gowenrw/astable_badge/art/2021-1.jpg

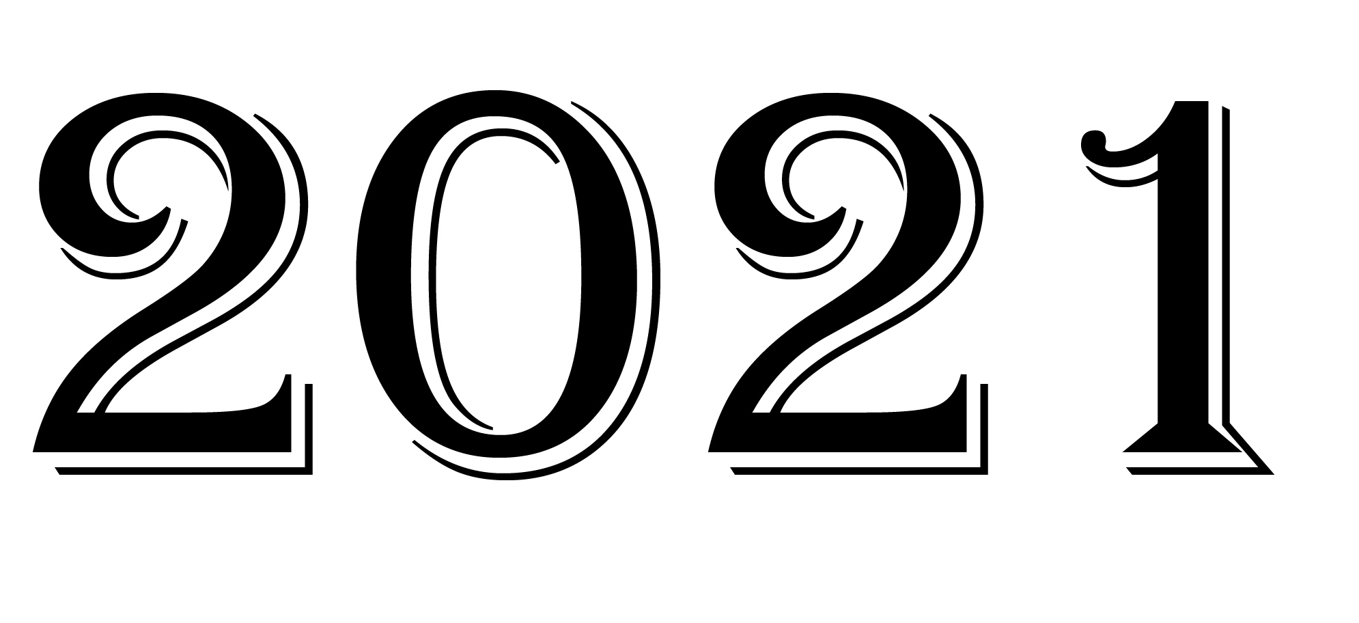
art/2021-1.jpg
