gowenrw/astable_badge/art/CyberDolphin-1-01.jpg

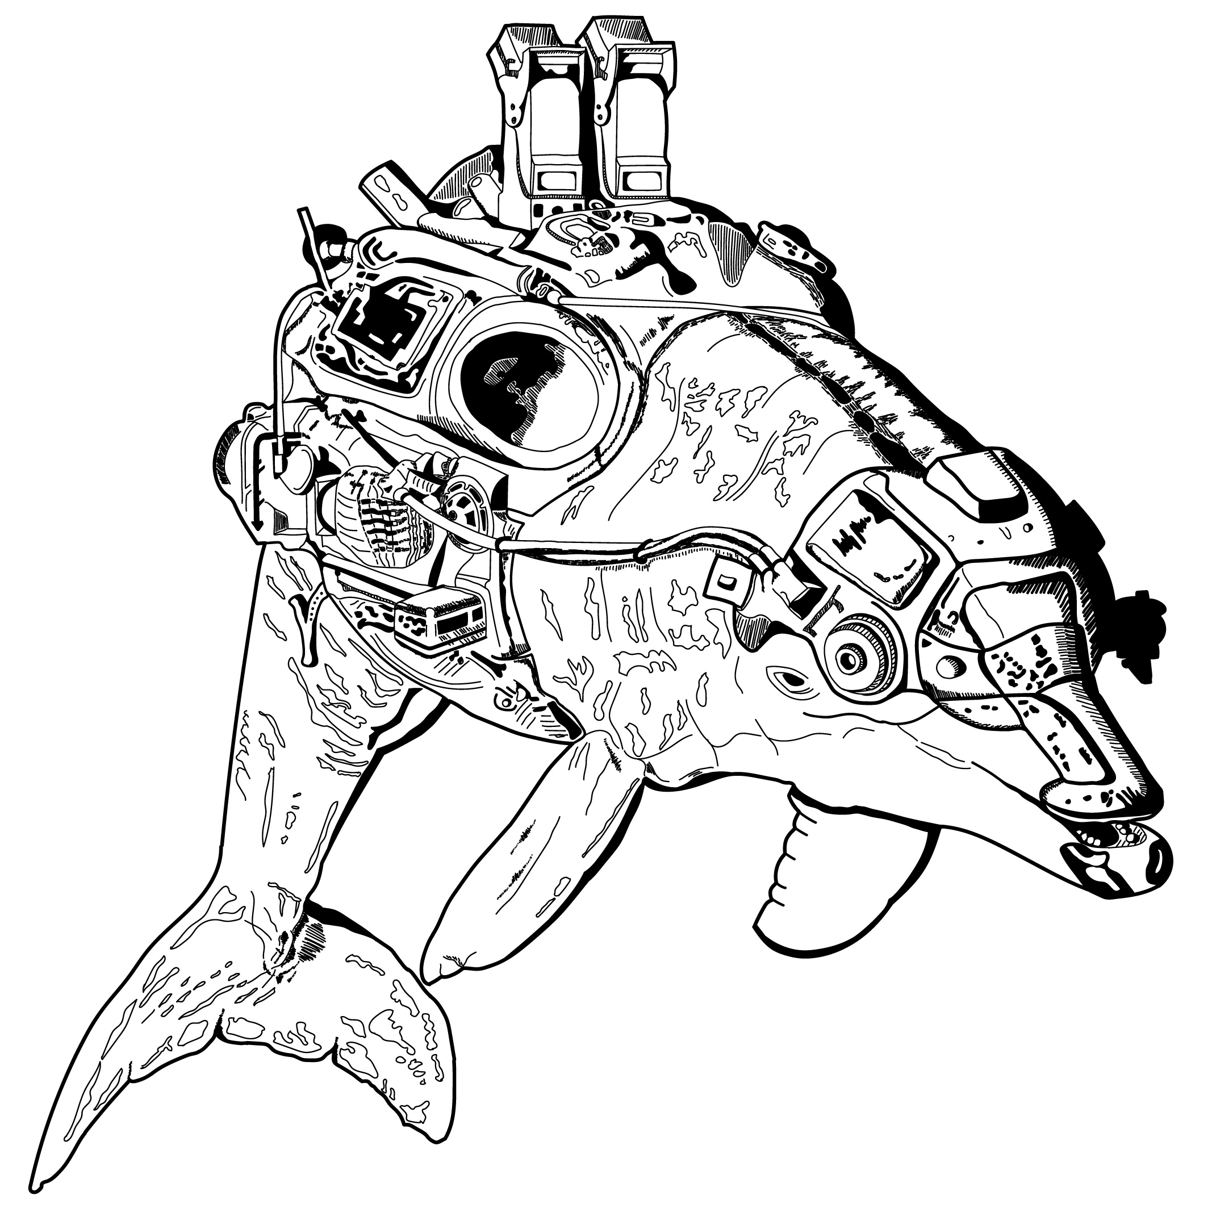
art/CyberDolphin-1-01.jpg
