gowenrw/astable_badge/art/inspiration/CyberDolphin.jpg

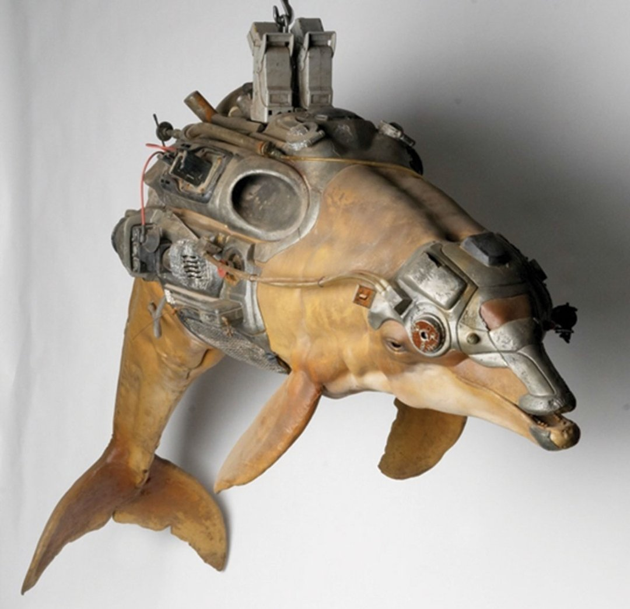
art/inspiration/CyberDolphin.jpg
