gowenrw/astable_badge/art/Lanyard-1-01.jpg

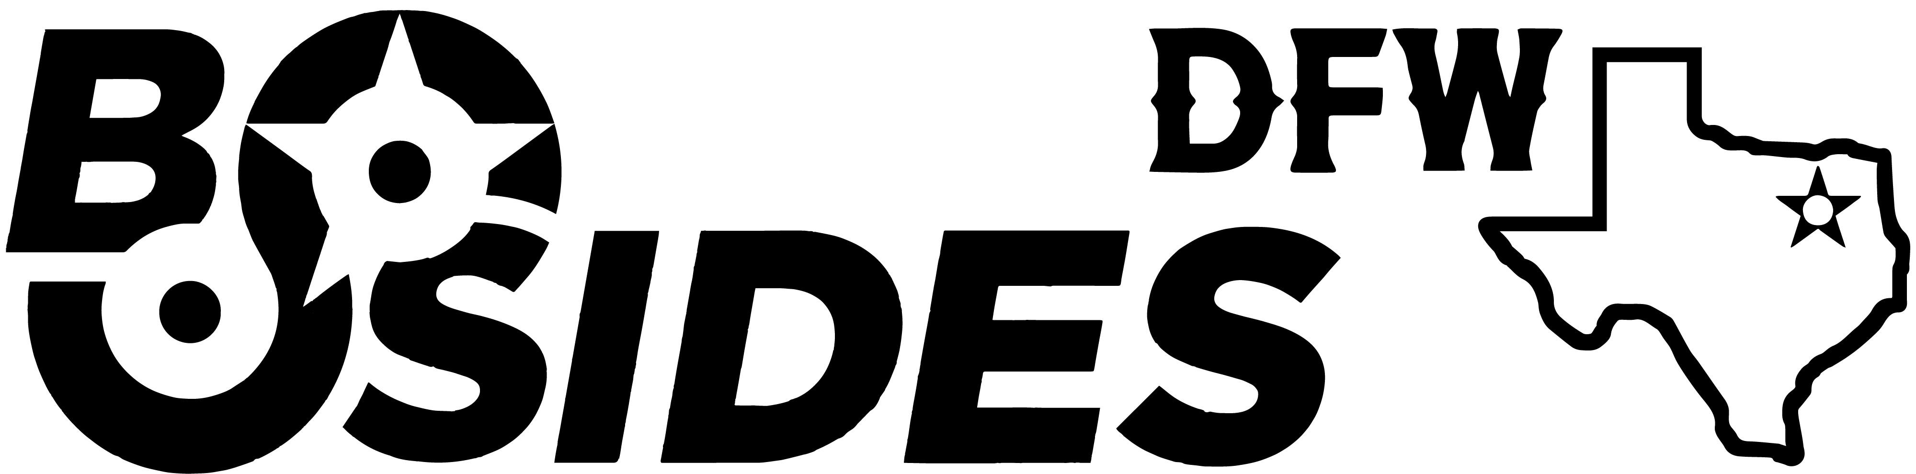
art/Lanyard-1-01.jpg
