gowenrw/astable_badge/eda/astable_dev/snapshots/astable_dev_3D_01.png

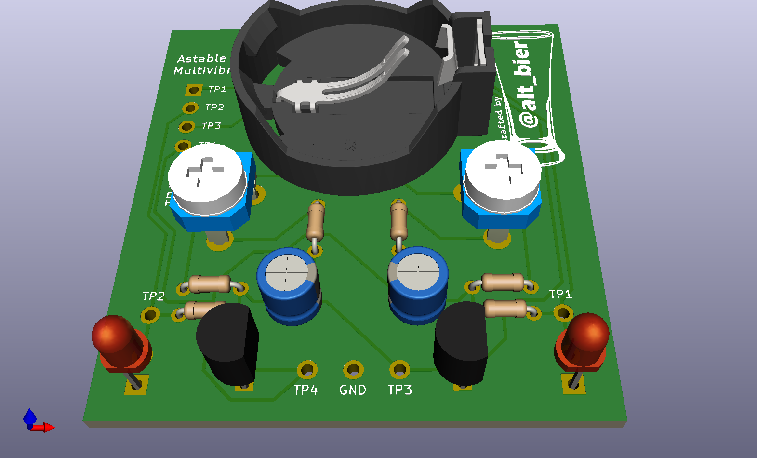
eda/astable_dev/snapshots/astable_dev_3D_01.png
