gowenrw/astable_badge/eda/astable_dev/3d_models/CP_Radial_D6.3mm_P2.50mm.step

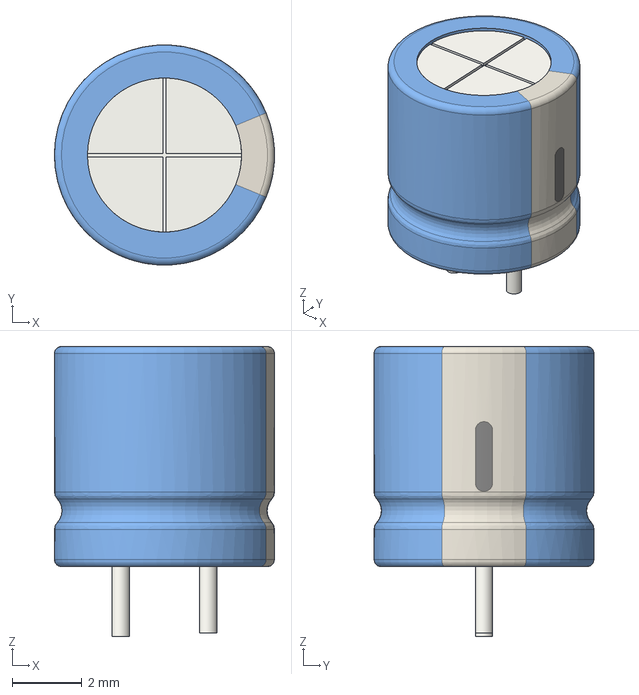
[picture p72: CAD file, 2021-08-17]
eda/astable_dev/3d_models/CP_Radial_D6.3mm_P2.50mm.step
6.30 x 6.30 x 8.30 mm
