gowenrw/astable_badge/eda/astable_badge/3d_models/PinHeader_1x05_P2.54mm_Vertical.step

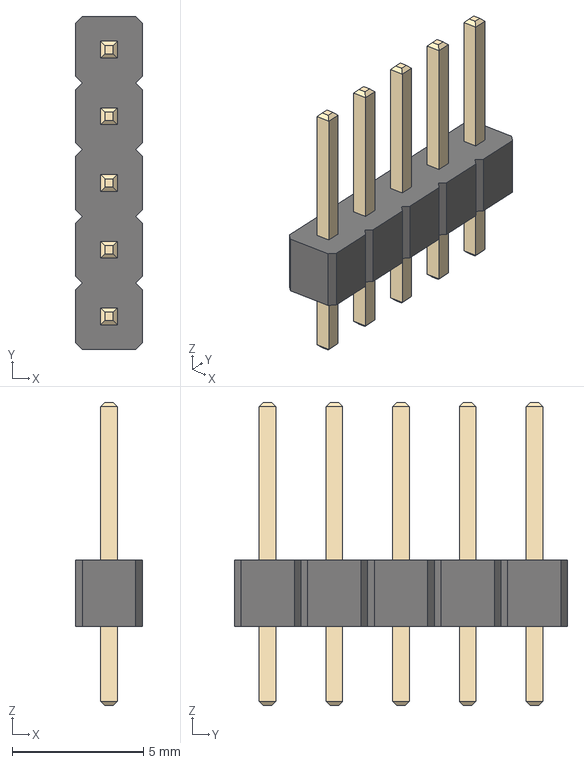
[picture p73: CAD file, 2021-08-19]
eda/astable_badge/3d_models/PinHeader_1x05_P2.54mm_Vertical.step
2.54 x 12.7 x 11.5 mm
