gowenrw/astable_badge/eda/astable_dev/3d_models/LED_D5.0mm-4_RGB.step

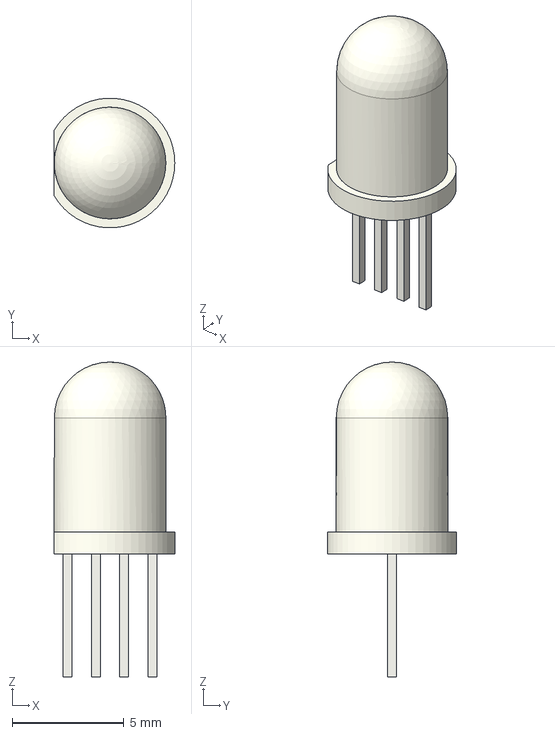
[picture p74: CAD file, 2021-08-17]
eda/astable_dev/3d_models/LED_D5.0mm-4_RGB.step
5.40 x 5.79 x 14.1 mm
