gowenrw/astable_badge/eda/astable_badge/3d_models/PinSocket_1x05_P2.54mm_Vertical.step

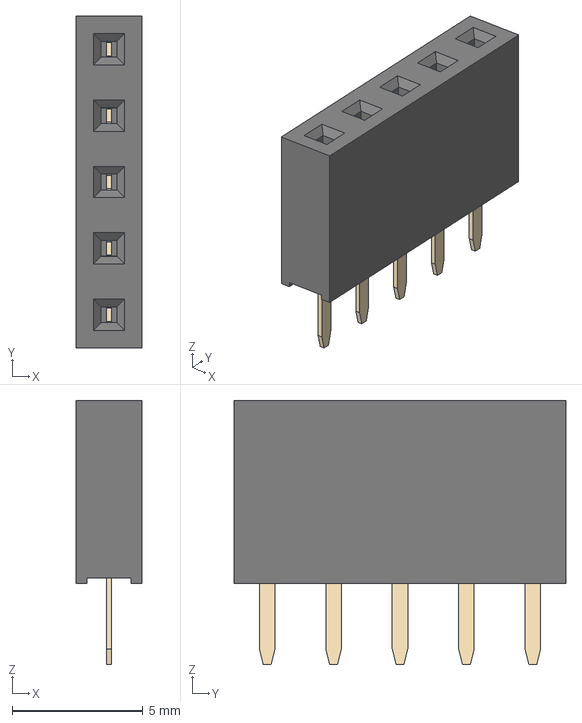
[picture p75: CAD file, 2021-08-19]
eda/astable_badge/3d_models/PinSocket_1x05_P2.54mm_Vertical.step
2.54 x 12.7 x 10.1 mm
