gowenrw/astable_badge/eda/astable_dev/3d_models/SW_SPDT_PCM12.step

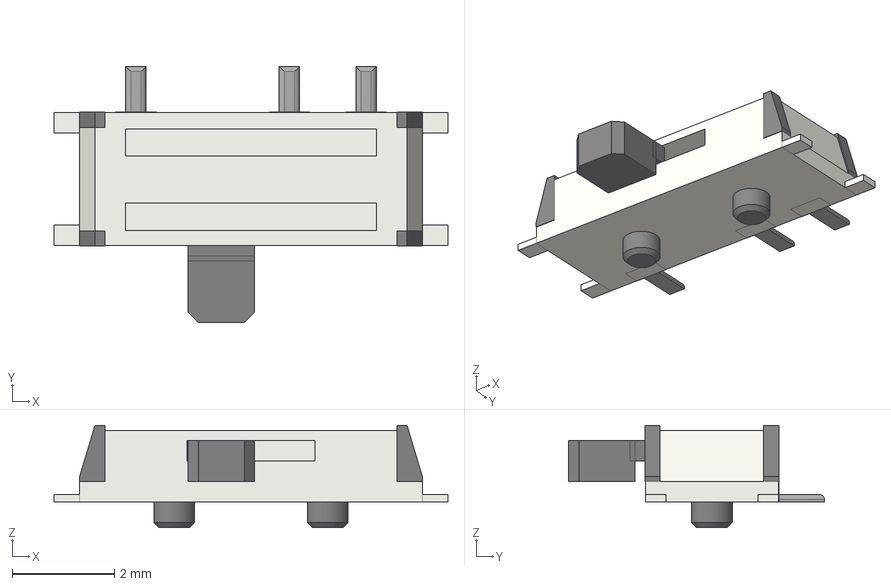
[picture p76: CAD file, 2021-08-17]
eda/astable_dev/3d_models/SW_SPDT_PCM12.step
7.70 x 5.00 x 2.00 mm
