gowenrw/astable_badge/eda/astable_badge/3d_models/PinHeader_1x01_P2.54mm_Horizontal.step

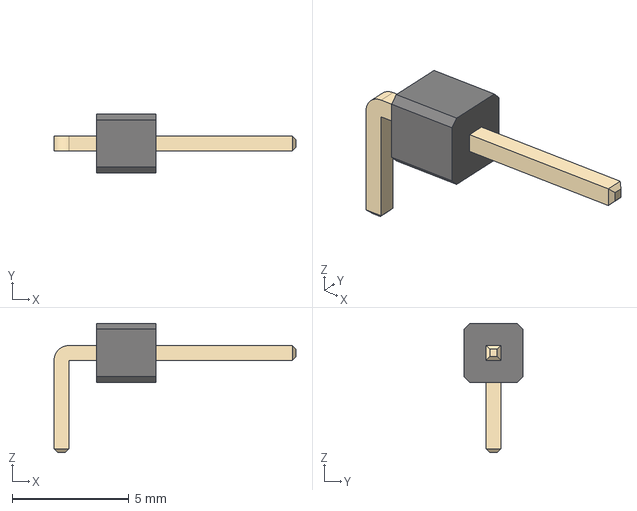
[picture p77: CAD file, 2021-08-19]
eda/astable_badge/3d_models/PinHeader_1x01_P2.54mm_Horizontal.step
10.4 x 2.54 x 5.54 mm
