gowenrw/astable_badge/eda/astable_badge/3d_models/PinSocket_1x05_P2.54mm_Horizontal.step

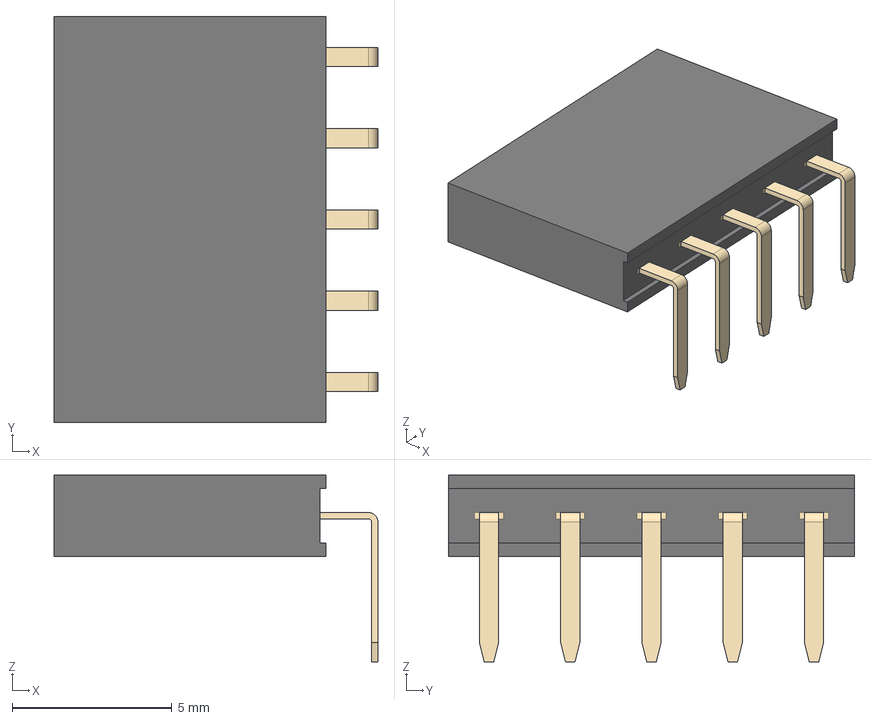
[picture p79: CAD file, 2021-08-19]
eda/astable_badge/3d_models/PinSocket_1x05_P2.54mm_Horizontal.step
10.1 x 12.7 x 5.84 mm
