gowenrw/astable_badge/eda/astable_dev/3d_models/LED_D5.0mm.step

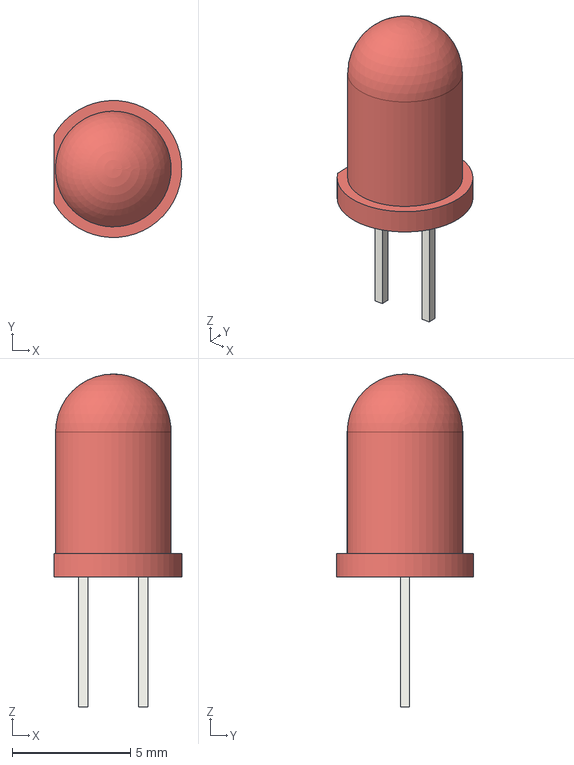
[picture p80: CAD file, 2021-08-17]
eda/astable_dev/3d_models/LED_D5.0mm.step
5.40 x 5.79 x 14.1 mm
