gowenrw/astable_badge/eda/astable_badge/3d_models/TO-92_Inline.step

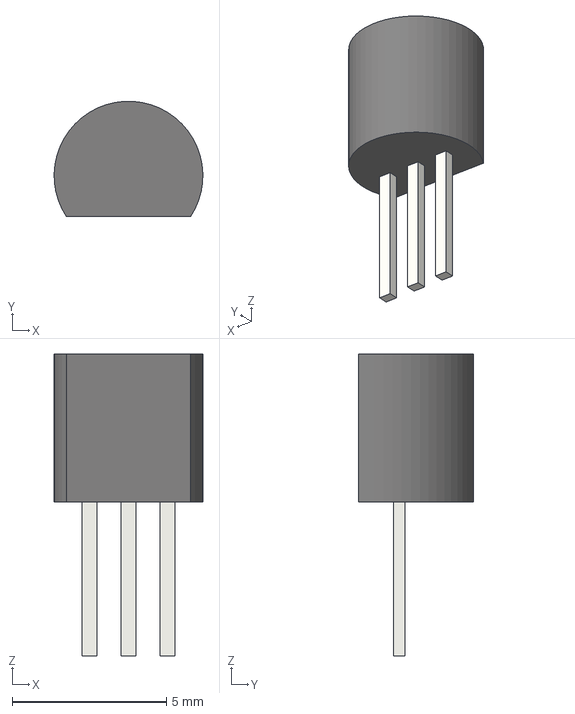
[picture p81: CAD file, 2021-08-18]
eda/astable_badge/3d_models/TO-92_Inline.step
4.83 x 3.74 x 9.80 mm
