gowenrw/astable_badge/eda/astable_dev/3d_models/C_0805_2012Metric.step

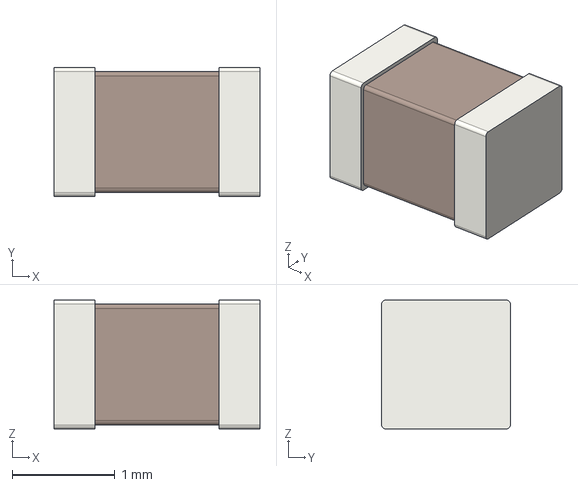
[picture p82: CAD file, 2021-08-17]
eda/astable_dev/3d_models/C_0805_2012Metric.step
2.00 x 1.25 x 1.25 mm
