gowenrw/astable_badge/eda/astable_badge/3d_models/Battery_Holder_CR2032_BS-2-1.stp

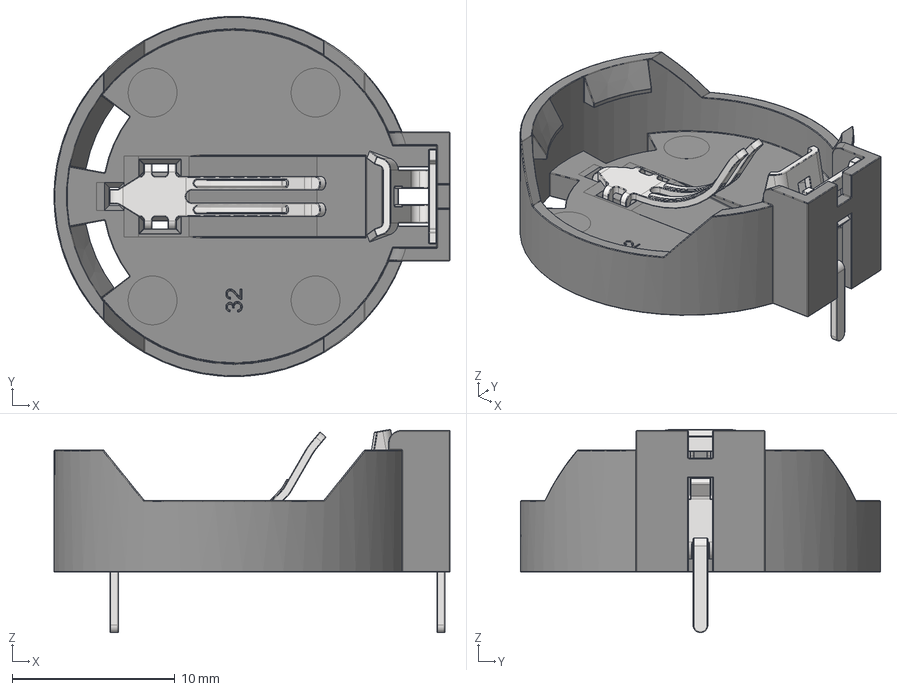
[picture p83: CAD file, 2021-08-18]
eda/astable_badge/3d_models/Battery_Holder_CR2032_BS-2-1.stp
24.3 x 22.1 x 12.5 mm
