gowenrw/astable_badge/eda/astable_dev/3d_models/C_0603_1608Metric.step

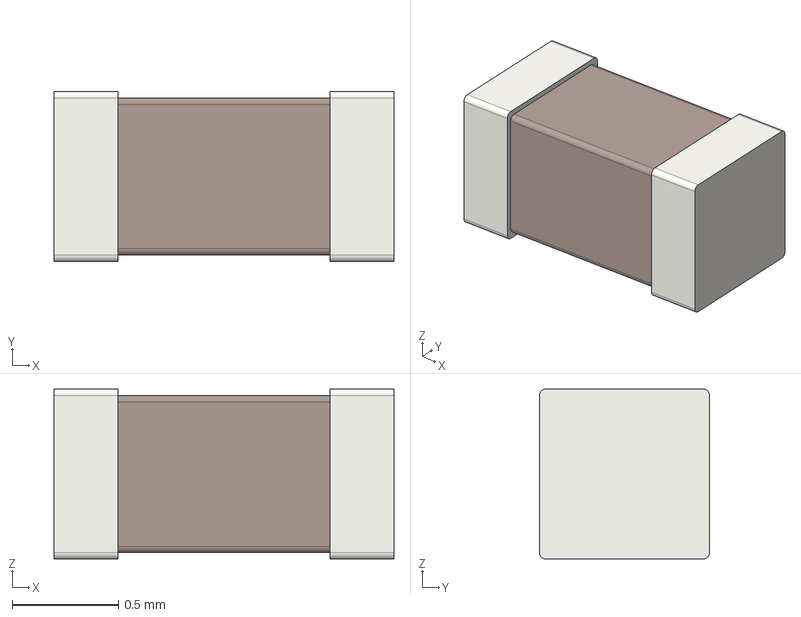
[picture p84: CAD file, 2021-08-17]
eda/astable_dev/3d_models/C_0603_1608Metric.step
1.60 x 0.8 x 0.8 mm
