gowenrw/astable_badge/eda/astable_badge/3d_models/CP_Radial_D5.0mm_P2.00mm.step

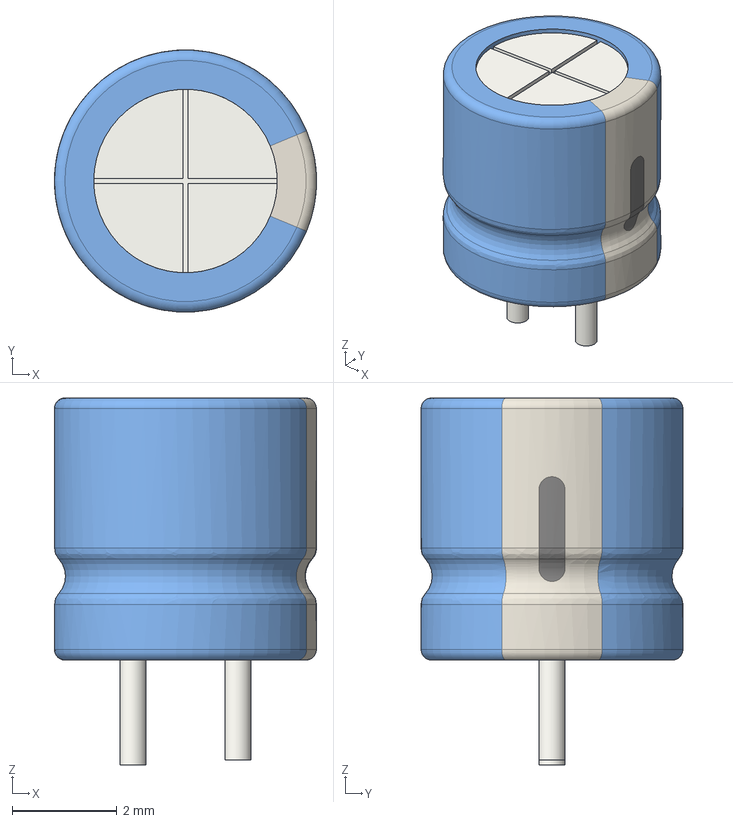
[picture p85: CAD file, 2021-08-18]
eda/astable_badge/3d_models/CP_Radial_D5.0mm_P2.00mm.step
5.00 x 5.00 x 7.00 mm
