gowenrw/astable_badge/eda/astable_dev/3d_models/RJ45_Amphenol_RJHSE-5080-56544.STEP

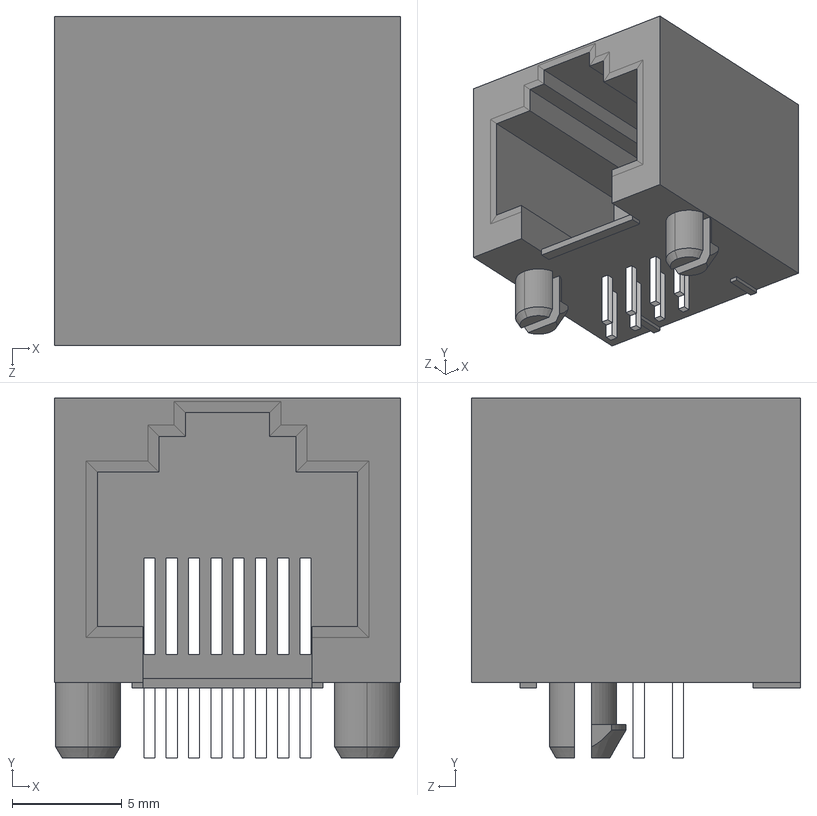
[picture p86: CAD file, 2021-08-17]
eda/astable_dev/3d_models/RJ45_Amphenol_RJHSE-5080-56544.STEP
15.7 x 16.4 x 15.0 mm
