gowenrw/astable_badge/eda/astable_dev/3d_models/SW_PUSH_6mm.step

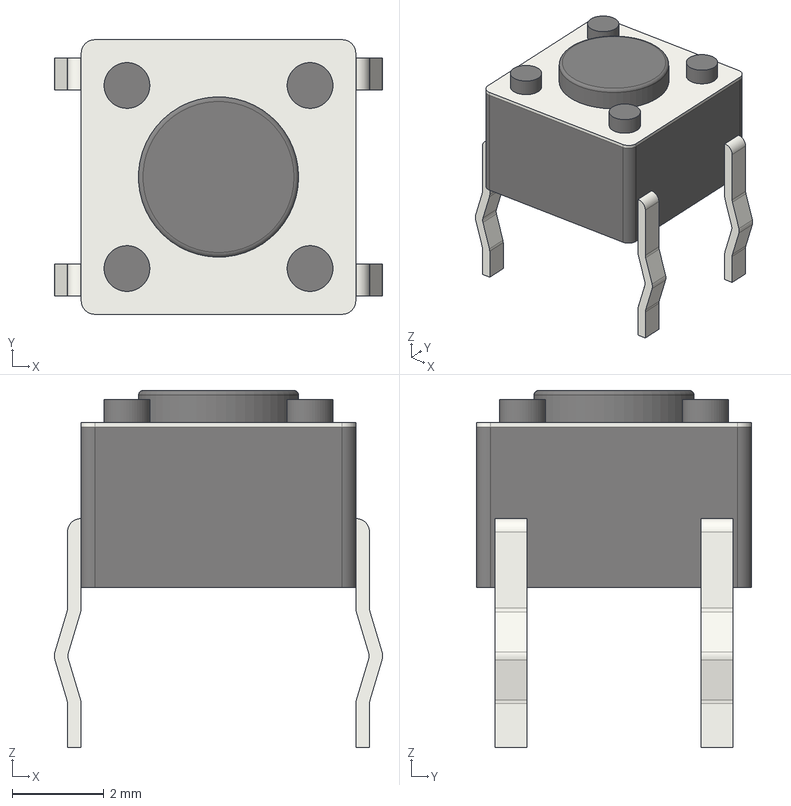
[picture p87: CAD file, 2021-08-17]
eda/astable_dev/3d_models/SW_PUSH_6mm.step
7.17 x 6.00 x 7.80 mm
