gowenrw/astable_badge/eda/astable_badge/3d_models/LED_D8.0mm.step

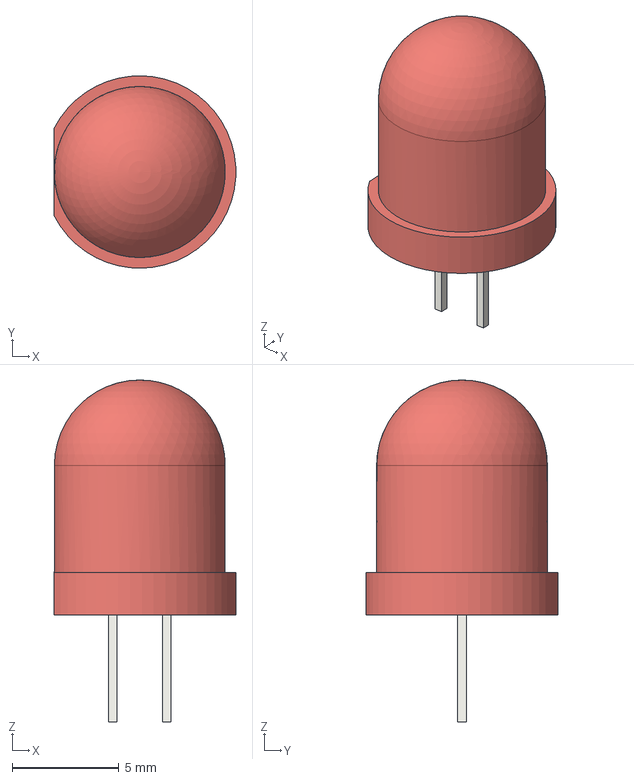
[picture p88: CAD file, 2021-08-17]
eda/astable_badge/3d_models/LED_D8.0mm.step
8.49 x 9.00 x 16.0 mm
