gowenrw/astable_badge/eda/astable_dev/3d_models/RJ45_Amphenol_RJHSE538X.step

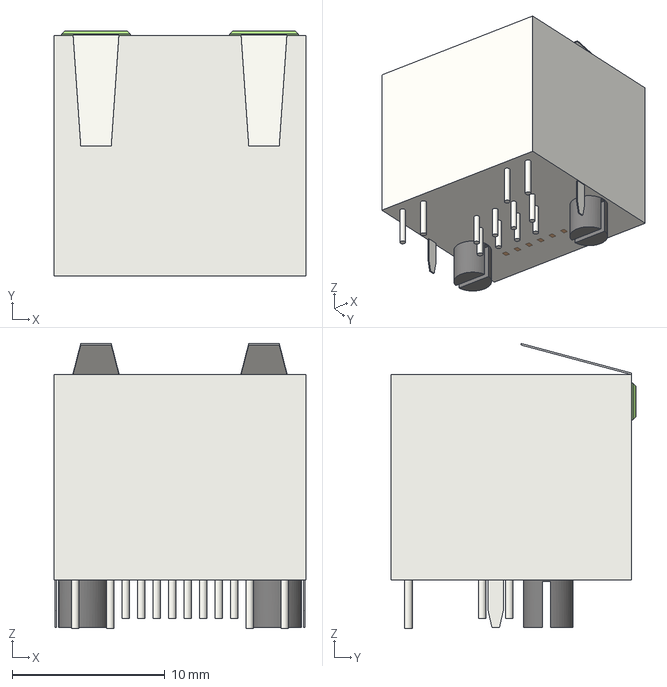
[picture p89: CAD file, 2021-08-17]
eda/astable_dev/3d_models/RJ45_Amphenol_RJHSE538X.step
16.5 x 16.1 x 18.7 mm
