gowenrw/astable_badge/eda/astable_dev/3d_models/R_0603_1608Metric.step

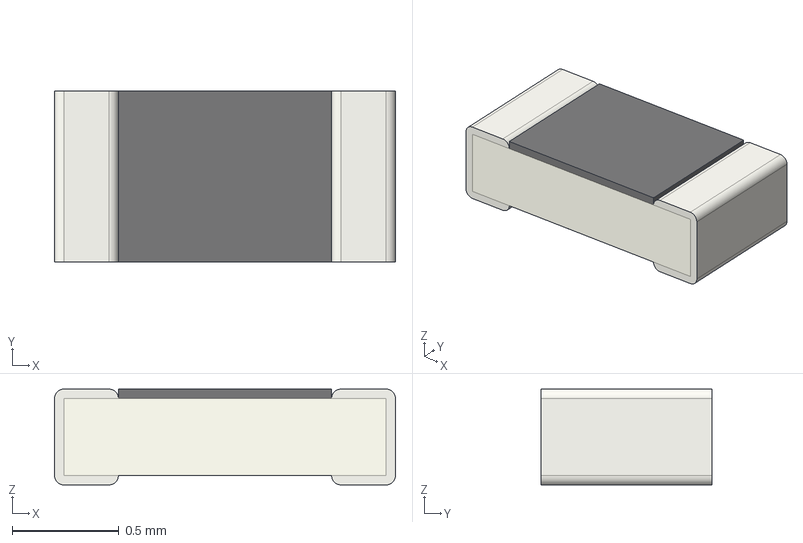
[picture p91: CAD file, 2021-08-17]
eda/astable_dev/3d_models/R_0603_1608Metric.step
1.60 x 0.8 x 0.45 mm
