gowenrw/astable_badge/eda/astable_badge/3d_models/PinHeader_1x08_P2.54mm_Horizontal.step

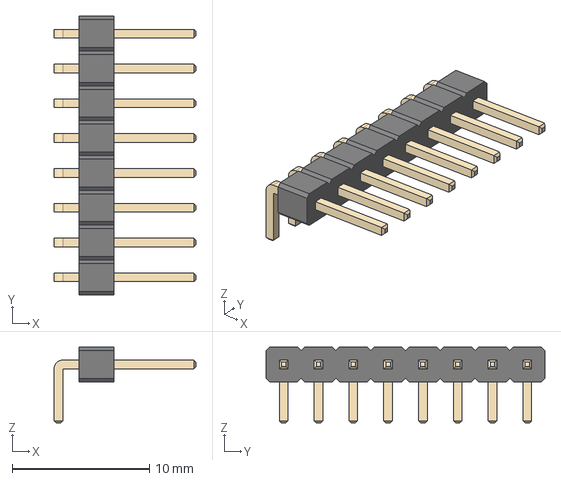
[picture p92: CAD file, 2021-08-17]
eda/astable_badge/3d_models/PinHeader_1x08_P2.54mm_Horizontal.step
10.4 x 20.3 x 5.54 mm
