gowenrw/astable_badge/eda/astable_dev/3d_models/R_0805_2012Metric.step

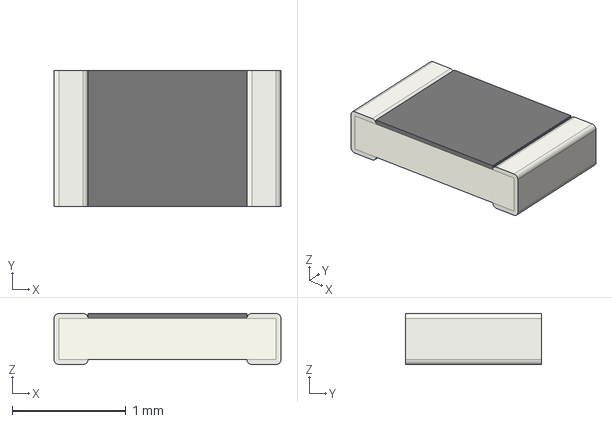
[picture p93: CAD file, 2021-08-17]
eda/astable_dev/3d_models/R_0805_2012Metric.step
2.00 x 1.20 x 0.45 mm
