gowenrw/astable_badge/eda/astable_dev/3d_models/Battery_Holder_3xAAA_Simple.step

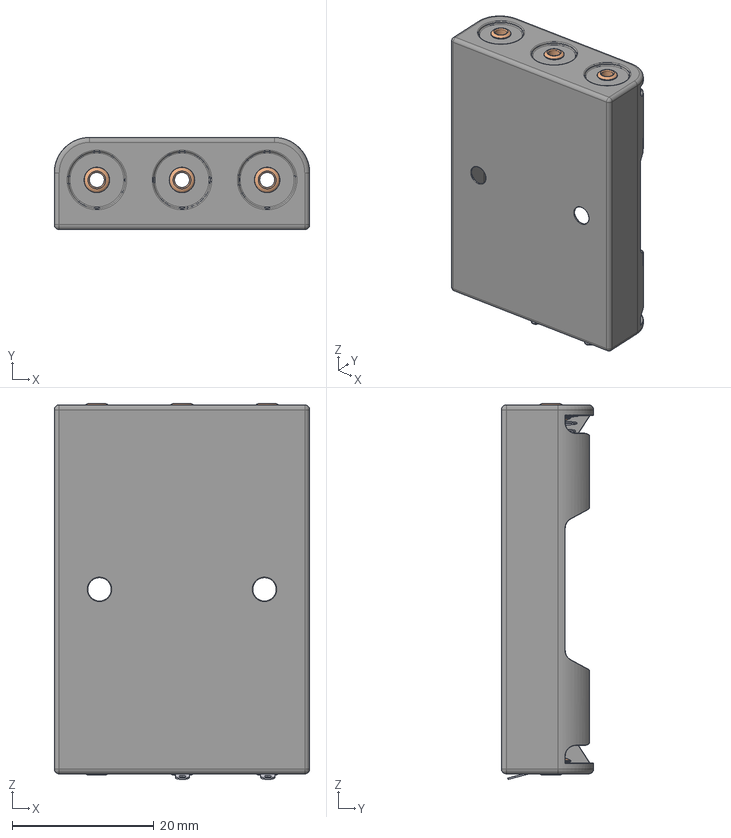
[picture p94: CAD file, 2021-08-17]
eda/astable_dev/3d_models/Battery_Holder_3xAAA_Simple.step
36.0 x 13.0 x 53.0 mm
