gowenrw/astable_badge/eda/astable_badge/3d_models/LED_0805_2012Metric_Castellated.step

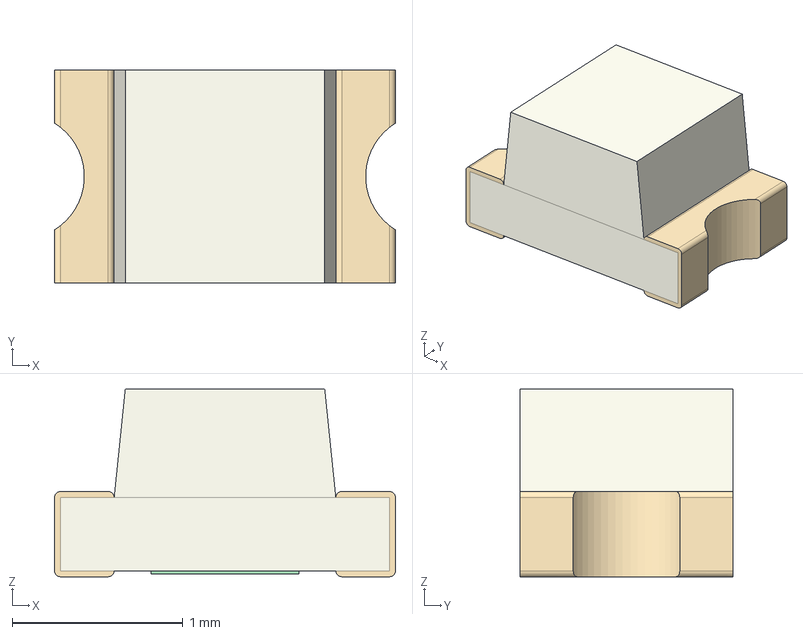
[picture p95: CAD file, 2021-08-17]
eda/astable_badge/3d_models/LED_0805_2012Metric_Castellated.step
2.00 x 1.25 x 1.10 mm
