gowenrw/astable_badge/eda/astable_dev/3d_models/R_1206_3216Metric.step

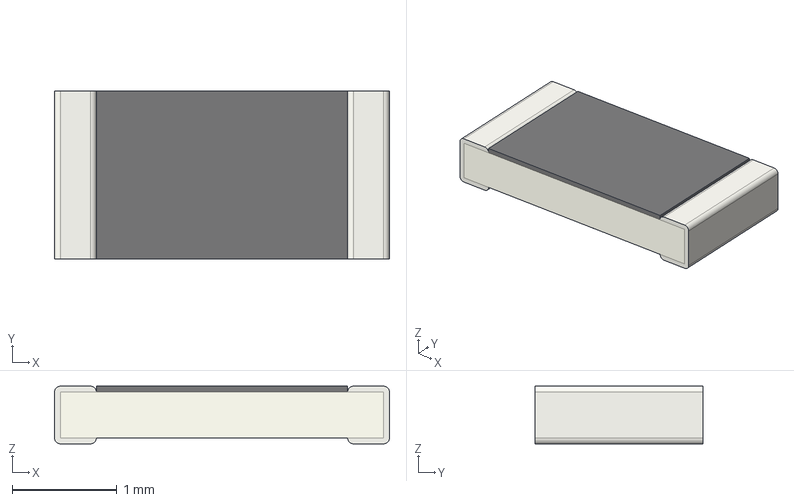
[picture p96: CAD file, 2021-08-17]
eda/astable_dev/3d_models/R_1206_3216Metric.step
3.20 x 1.60 x 0.55 mm
