gowenrw/astable_badge/eda/astable_dev/3d_models/USB_Micro-B_Molex_47346-0001.step

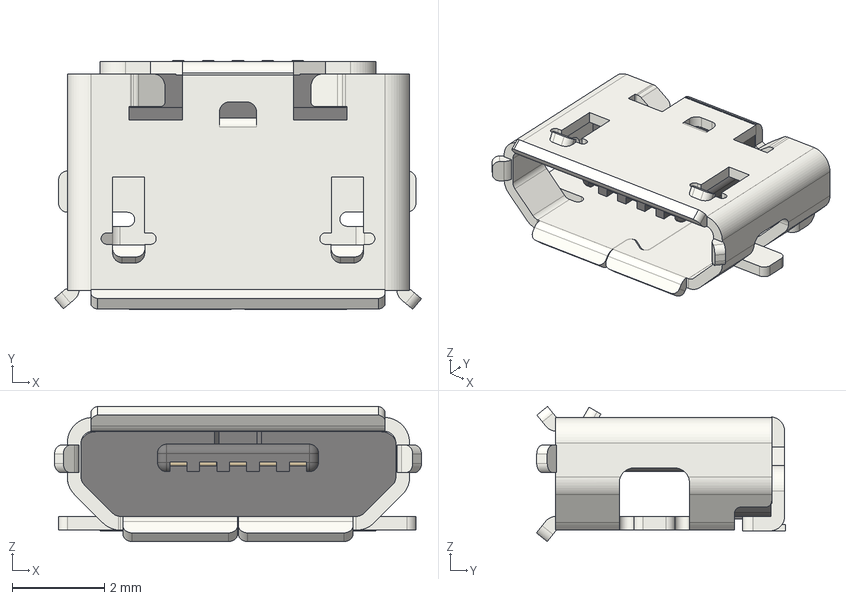
[picture p97: CAD file, 2021-08-17]
eda/astable_dev/3d_models/USB_Micro-B_Molex_47346-0001.step
7.98 x 5.42 x 2.94 mm
