gowenrw/astable_badge/eda/astable_dev/3d_models/TS2306A.step

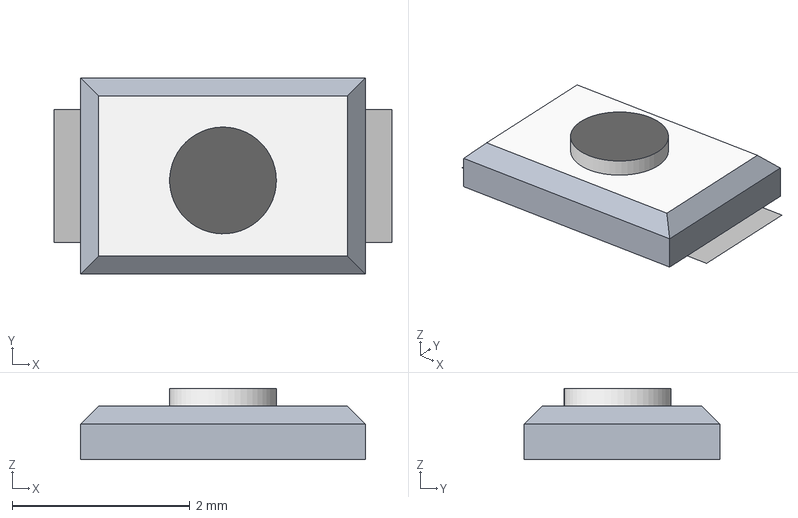
[picture p98: CAD file, 2021-08-17]
eda/astable_dev/3d_models/TS2306A.step
3.80 x 2.20 x 0.8 mm
Plane
