gowenrw/astable_badge/eda/astable_badge/3d_models/SOIC-16_3.9x9.9mm_P1.27mm.step

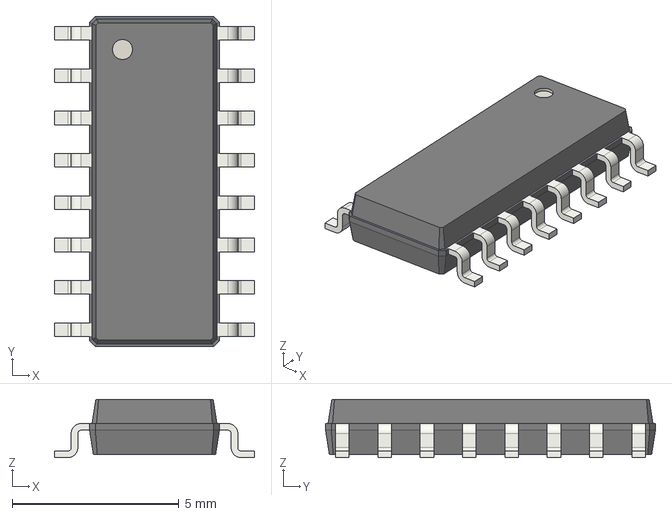
[picture p99: CAD file, 2021-08-17]
eda/astable_badge/3d_models/SOIC-16_3.9x9.9mm_P1.27mm.step
6.00 x 9.90 x 1.75 mm
