gowenrw/astable_badge/eda/astable_dev/3d_models/PinHeader_1x02_P2.54mm_Vertical.step

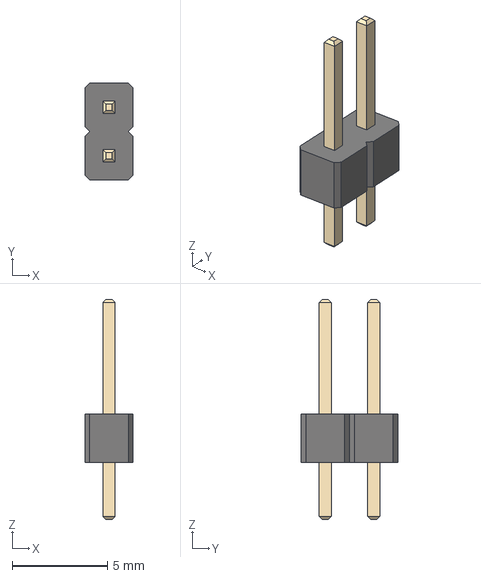
[picture p100: CAD file, 2021-08-17]
eda/astable_dev/3d_models/PinHeader_1x02_P2.54mm_Vertical.step
2.54 x 5.08 x 11.5 mm
