gowenrw/astable_badge/eda/astable_dev/3d_models/C_1206_3216Metric.step

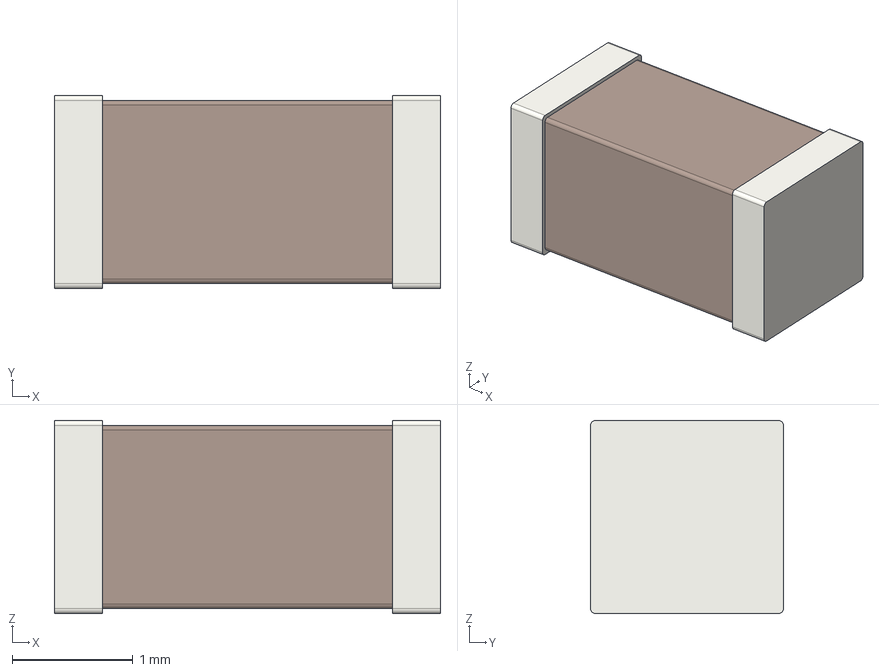
[picture p101: CAD file, 2021-08-17]
eda/astable_dev/3d_models/C_1206_3216Metric.step
3.20 x 1.60 x 1.60 mm
